brainboxemb/2026-006-01.cad.HUB75-display-frame/v1.2/out/png/hub75-display-frame-middle-panel-fit-section.png

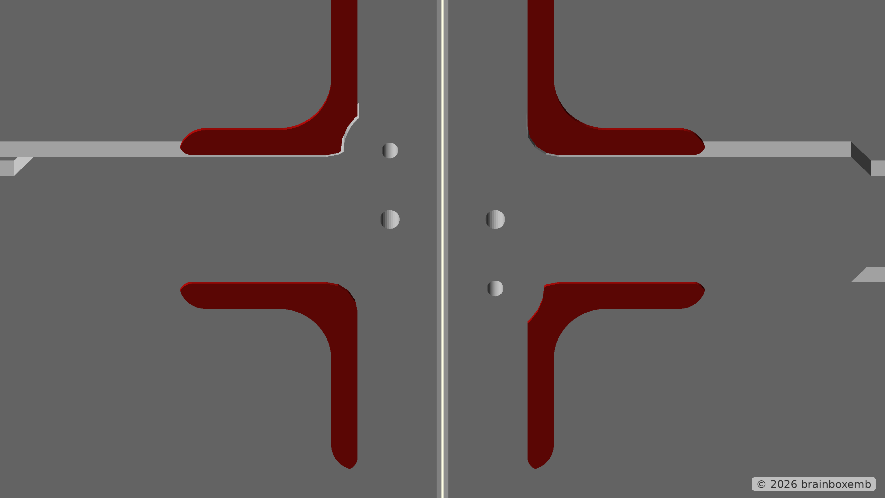
v1.2/out/png/hub75-display-frame-middle-panel-fit-section.png
