brainboxemb/2026-006-01.cad.HUB75-display-frame/v1.2/out/reference/hub75-display-frame-panel-reference.png

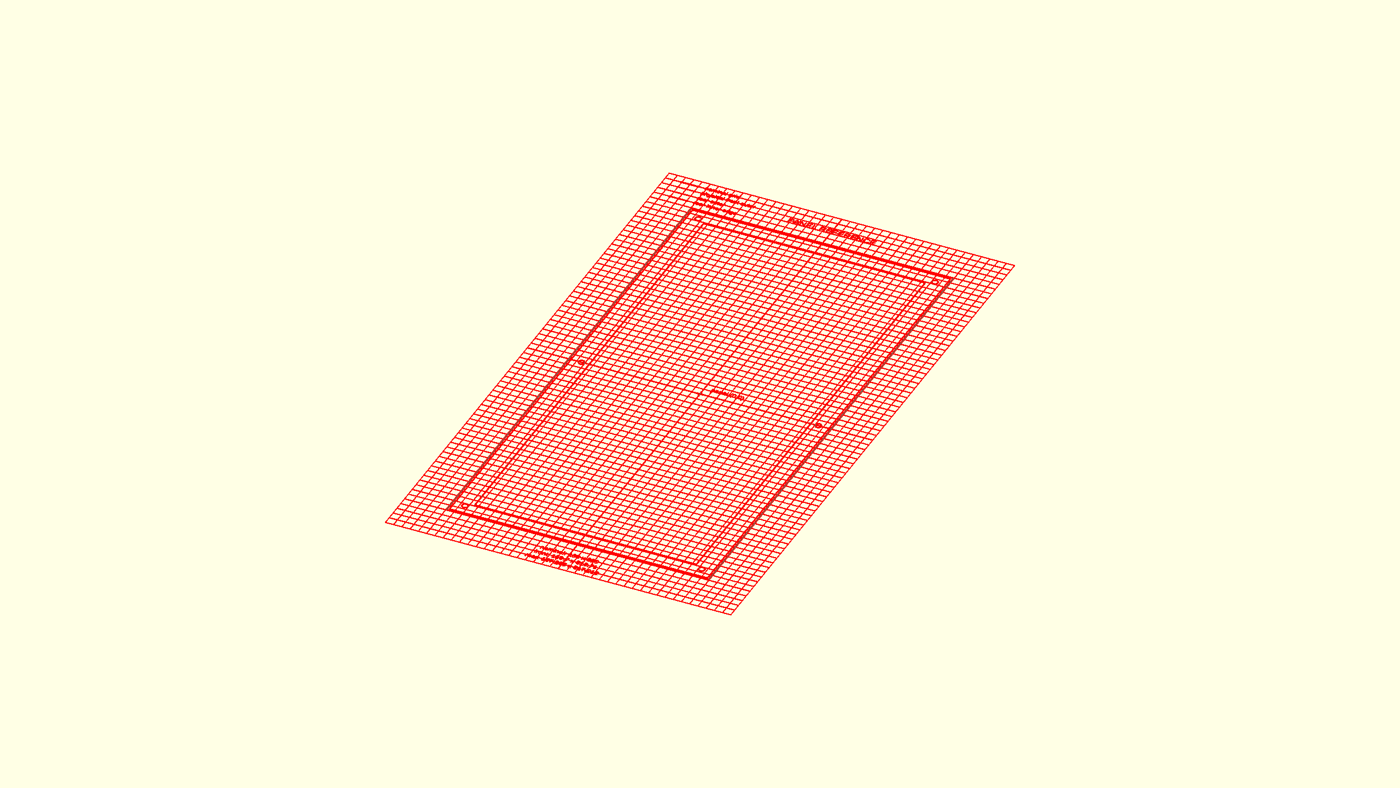
v1.2/out/reference/hub75-display-frame-panel-reference.png
