brainboxemb/2026-006-01.cad.HUB75-display-frame/cad/v1.2/exports/horizontal_edge_panel_coupler.scad

// Printable internal horizontal edge panel coupler.
// The physical part is identical; the top/bottom distinction is only assembly orientation.
include <../config/project_config.scad>
use <../components/hub75_panel.scad>
use <../assemblies/couplers_assembly.scad>

project_horizontal_edge_panel_coupler(direction="top", screw_row_z=panel_hole_z_top());
