brainboxemb/2026-006-01.cad.HUB75-display-frame/cad/v1.2/exports/middle_seam_coupler.scad

// HUB75 Display Frame - V1.2
// STL export entry point: middle seam coupler.
//
// The GitHub export action can export every *.scad file in exports/ without
// needing to know component internals. Project parameters remain mapped in the
// coupler assembly, so this entry point always matches the assembled design.

use <../assemblies/couplers_assembly.scad>

project_middle_coupler();
