brainboxemb/2026-006-01.cad.HUB75-display-frame/v1.2/cad/exports/corner_edge_panel_coupler_right_large.scad

// STL export entry - V1.2 LARGE right corner edge panel coupler.
include <../config/project_config.scad>
use <../components/hub75_panel.scad>
use <../assemblies/couplers_assembly.scad>

$coupler_design_profile = "large";
project_corner_edge_panel_coupler(side="right", direction="top", screw_row_z=panel_hole_z_top());
