brainboxemb/2026-006-01.cad.HUB75-display-frame/v1.2/cad/exports/middle_panel_coupler_small.scad

// STL export entry - V1.2 SMALL middle panel coupler.
include <../config/project_config.scad>
use <../assemblies/couplers_assembly.scad>

$coupler_design_profile = "small";
project_middle_panel_coupler();
