brainboxemb/2026-006-01.cad.HUB75-display-frame/v1.2/cad/renders/couplers_large_horizontal_edge.scad

// V1.2 LARGE horizontal edge panel coupler.
include <../config/project_config.scad>
use <../components/hub75_panel.scad>
use <../assemblies/couplers_assembly.scad>

$coupler_design_profile = "large";
$vpt = [0, 0, 0];
$vpr = [90, 0, 180];
$vpd = 270;

project_horizontal_edge_panel_coupler(direction="top", screw_row_z=panel_hole_z_top());
