brainboxemb/2026-006-01.cad.HUB75-display-frame/v1.2/cad/renders/couplers_small_side_by_side.scad

// V1.2 SMALL coupler comparison - side by side.
include <../config/project_config.scad>
use <../assemblies/coupler_comparison_assembly.scad>

$coupler_design_profile = "small";

$vpt = [0, 0, 0];
$vpr = [90, 0, 180];
$vpd = 560;

coupler_comparison_side_by_side(show_grid=true, grid_major=10, grid_half_step=true);
