brainboxemb/2026-006-01.cad.HUB75-display-frame/v1.2/cad/renders/exploded_rear.scad

// Official V1.2 exploded render - straight rear view.
// This view keeps all exploded offsets easy to compare against the normal rear view.

include <../config/project_config.scad>

$coupler_design_profile = "medium"; // Canonical V1.2 documentation profile.
use <../assemblies/display_assembly.scad>

exploded_render_distance = 40;

$vpt = [0, 0, 0];
$vpr = [90, 0, 180];
$vpd = 1200;

display_assembly(
    orientation_visible=false,
    panel_numbers_visible=false,
    in_out_labels_visible=false,
    explode_distance=exploded_render_distance
);
