brainboxemb/2026-006-01.cad.HUB75-display-frame/v1.2/cad/renders/front.scad

// Official V1.2 README render - front view.
// Camera values are deliberately stored in CAD so CI and local renders match.

include <../config/project_config.scad>

$coupler_design_profile = "medium"; // Canonical V1.2 documentation profile.
use <../assemblies/display_assembly.scad>

$vpt = [0, 0, 0];
$vpr = [90, 0, 0];
$vpd = 1200;

display_assembly(
    orientation_visible=false,
    panel_numbers_visible=false,
    in_out_labels_visible=false
);
