brainboxemb/2026-006-01.cad.HUB75-display-frame/v1.2/cad/renders/front_angled.scad

// Official V1.2 README render - front three-quarter view.
// A small angle makes frame depth, panel thickness and tube clamps easier to read.

include <../config/project_config.scad>

$coupler_design_profile = "medium"; // Canonical V1.2 documentation profile.
use <../assemblies/display_assembly.scad>

$vpt = [0, 0, 0];
$vpr = [85, 0, 40];
$vpd = 1050;

display_assembly(
    orientation_visible=false,
    panel_numbers_visible=false,
    in_out_labels_visible=false
);
